whowechina/voltex_pico/doc/m2_8mm.jpg

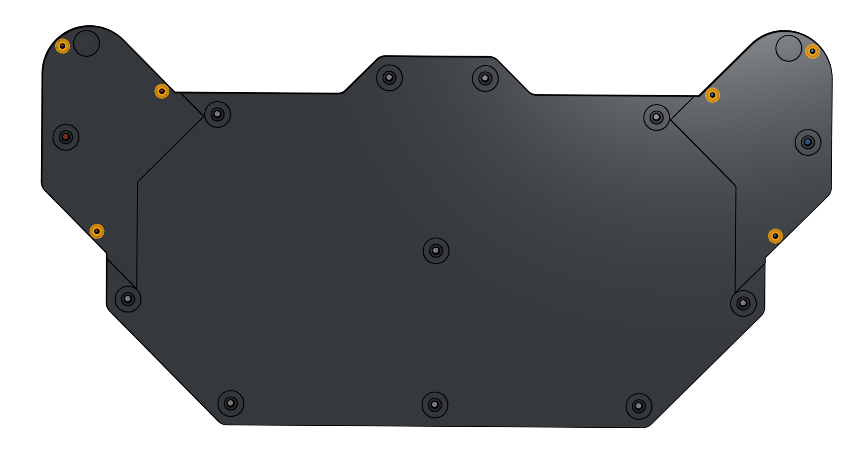
doc/m2_8mm.jpg
