whowechina/voltex_pico/PCB/jumbo/3dmodels/Raspberry Pi Pico-R3.step

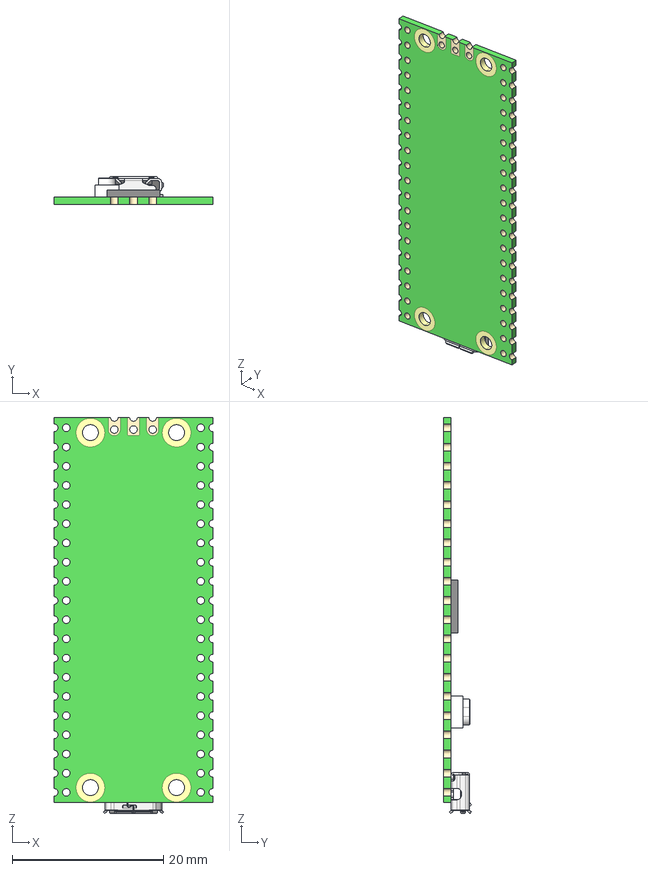
[picture p35: CAD file, 2026-08-16]
PCB/jumbo/3dmodels/Raspberry Pi Pico-R3.step
21.0 x 3.69 x 52.4 mm
PCB, Raspberry Pi Pico-R3
MicroUSB Port, Raspberry Pi Pico-R3
MicroUSB Port, Raspberry Pi Pico-R004
RP2040 Microcontroller, Raspberry Pi Pico-R3
SW1, Tact Switch, Raspberry Pi Pico-R3
