whowechina/voltex_pico/Production/3DPrint/Voltex Pico - Magnet Seat.stl

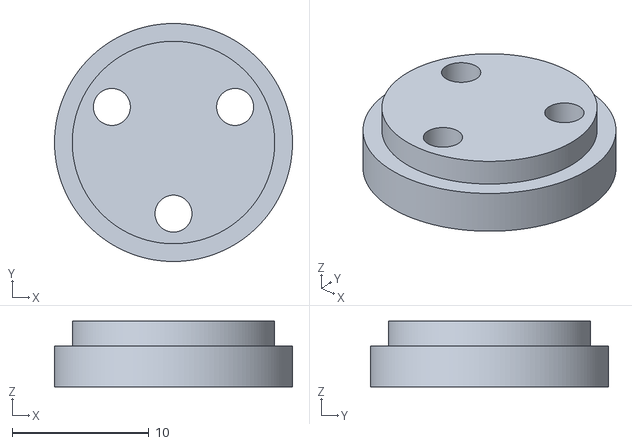
[picture p36: CAD file, 2025-12-08]
Production/3DPrint/Voltex Pico - Magnet Seat.stl
17.4 x 17.4 x 4.80
