whowechina/voltex_pico/PCB/jumbo/3dmodels/FPC6P_1.0mm_Bottom_Contact_Flip.stp

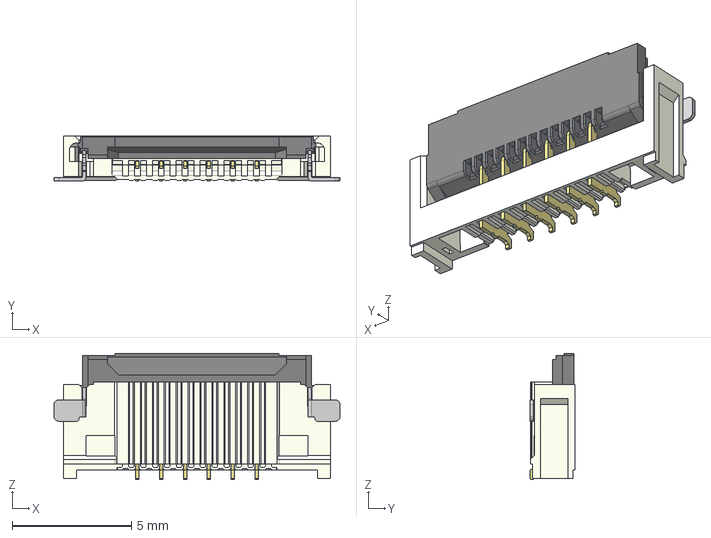
[picture p37: CAD file, 2026-03-18]
PCB/jumbo/3dmodels/FPC6P_1.0mm_Bottom_Contact_Flip.stp
12.0 x 1.90 x 5.30 mm
