whowechina/voltex_pico/Production/3DPrint/Voltex Pico - Left Wing Cover_Insert.stl

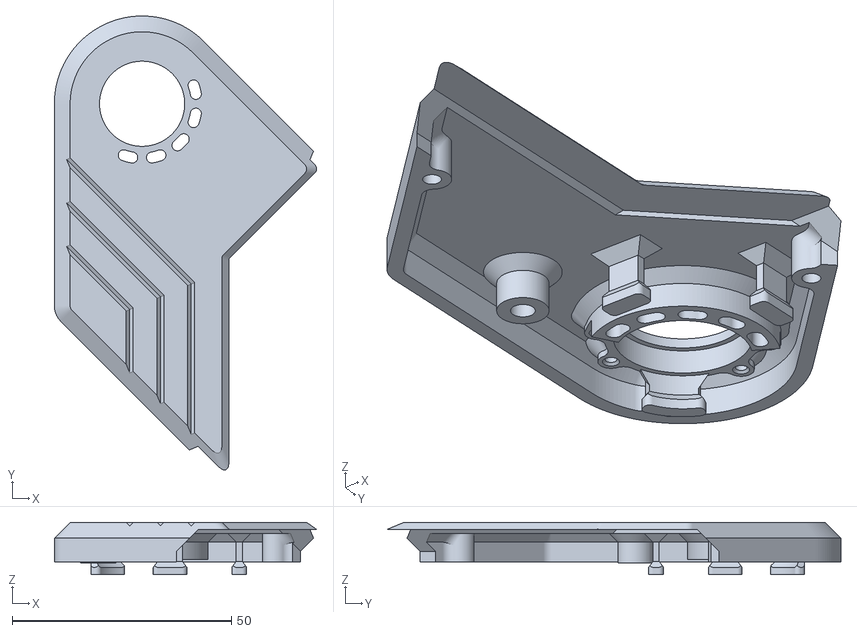
[picture p38: CAD file, 2025-12-07]
Production/3DPrint/Voltex Pico - Left Wing Cover_Insert.stl
59.8 x 103.4 x 11.9
