whowechina/voltex_pico/PCB/jumbo/3dmodels/skhhbva010.stp

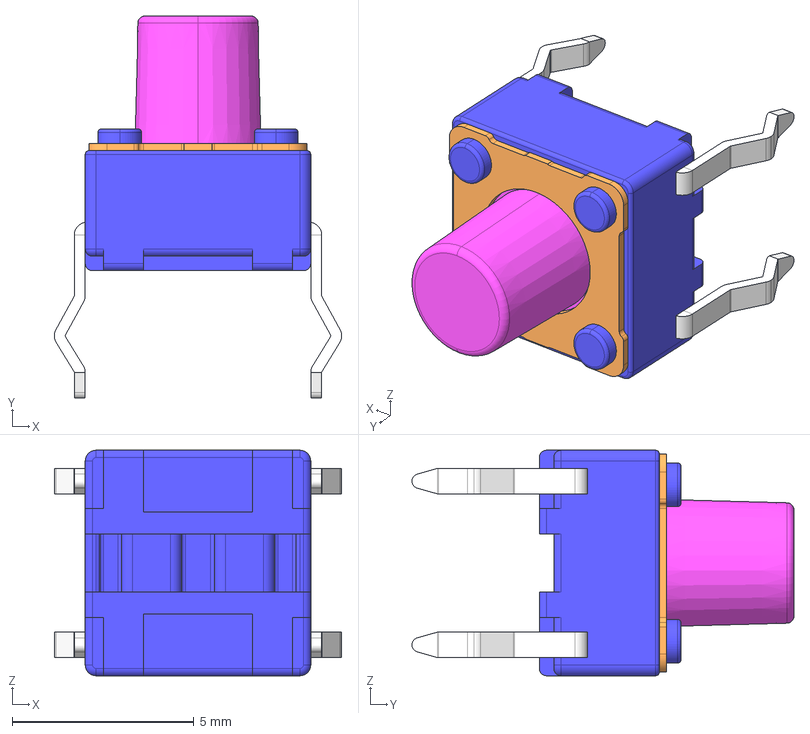
[picture p39: CAD file, 2025-06-14]
PCB/jumbo/3dmodels/skhhbva010.stp
7.90 x 10.5 x 6.20 mm
