whowechina/voltex_pico/Production/3DPrint/Voltex Pico - BT Choc V2_TallFix.stl

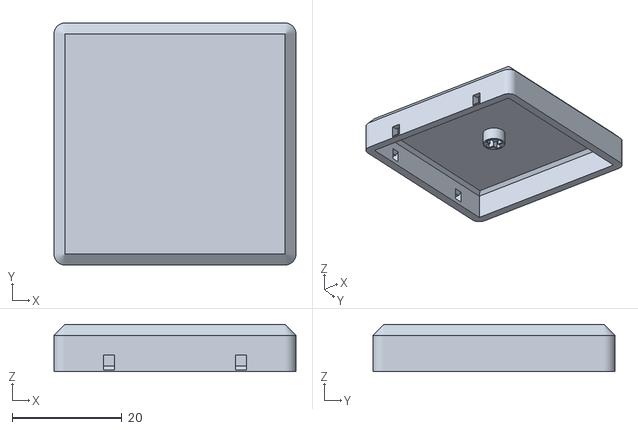
[picture p40: CAD file, 2025-12-07]
Production/3DPrint/Voltex Pico - BT Choc V2_TallFix.stl
44.0 x 44.0 x 8.60
