whowechina/voltex_pico/PCB/jumbo/3dmodels/skhhana010.stp

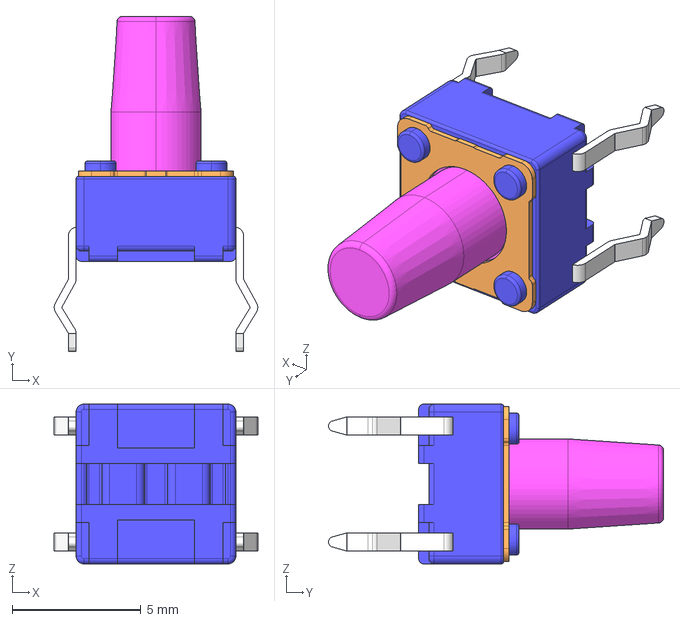
[picture p41: CAD file, 2025-06-14]
PCB/jumbo/3dmodels/skhhana010.stp
7.90 x 13.0 x 6.20 mm
