whowechina/voltex_pico/Production/3DPrint/Voltex Pico - FX-L Choc V2_TallFix.stl

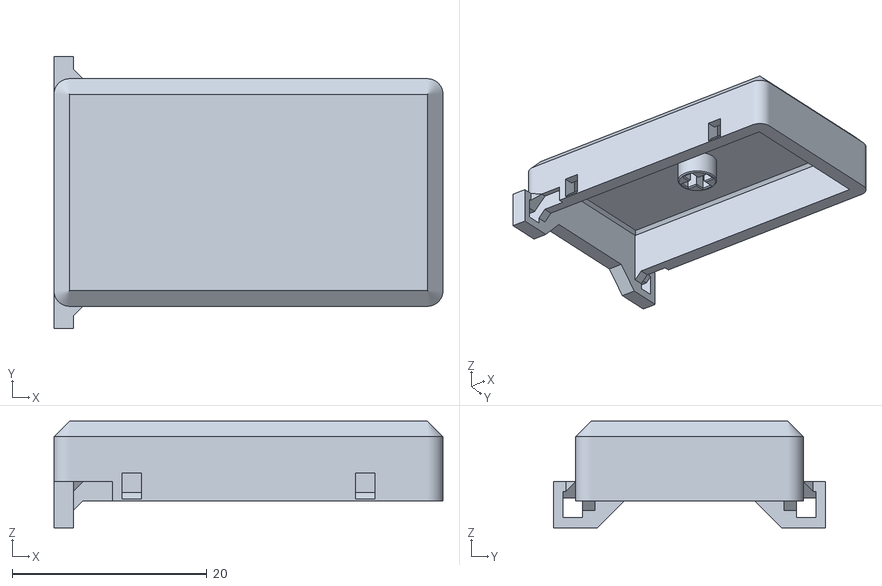
[picture p42: CAD file, 2025-12-07]
Production/3DPrint/Voltex Pico - FX-L Choc V2_TallFix.stl
40.0 x 28.0 x 11.0
