whowechina/voltex_pico/PCB/jumbo/3dmodels/SW_Hotswap_Kailh_MX.stp

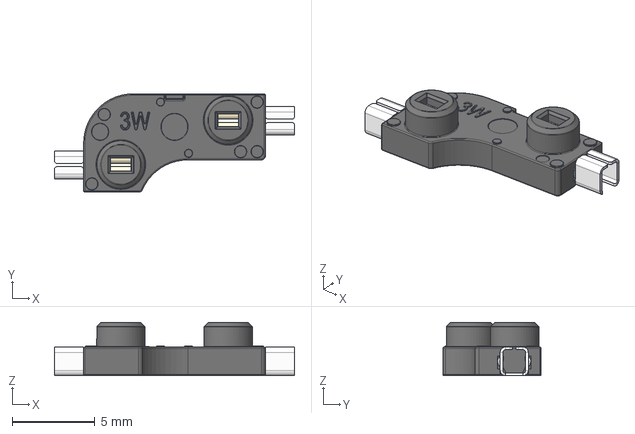
[picture p43: CAD file, 2025-05-26]
PCB/jumbo/3dmodels/SW_Hotswap_Kailh_MX.stp
14.5 x 5.95 x 3.22 mm
