whowechina/voltex_pico/PCB/jumbo/3dmodels/User Library-WS2812-4020.step

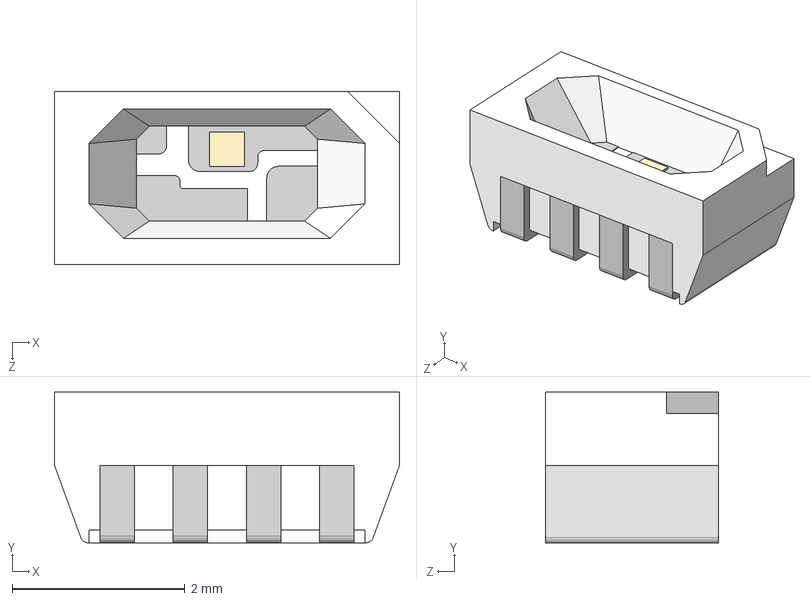
[picture p44: CAD file, 2025-05-26]
PCB/jumbo/3dmodels/User Library-WS2812-4020.step
4.00 x 1.75 x 2.00 mm
