whowechina/voltex_pico/PCB/jumbo/3dmodels/User Library-WS2812-2020.step

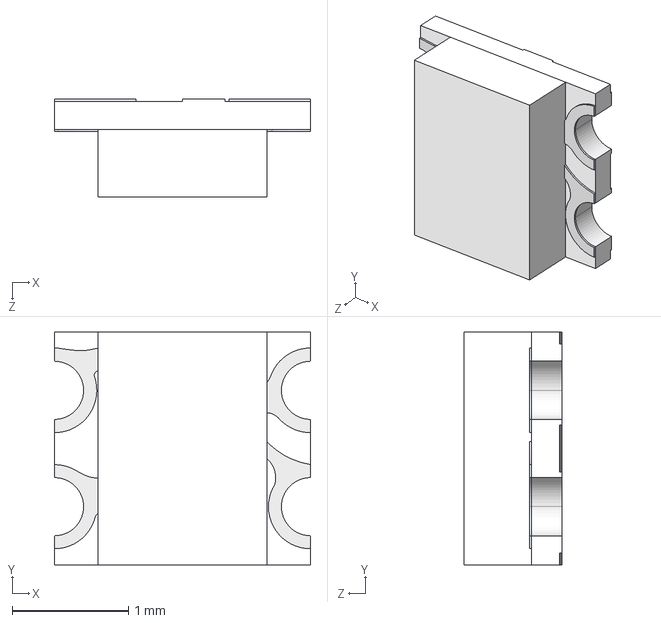
[picture p45: CAD file, 2025-05-26]
PCB/jumbo/3dmodels/User Library-WS2812-2020.step
2.20 x 2.00 x 0.84 mm
