whowechina/voltex_pico/PCB/jumbo/3dmodels/WS2812B.step

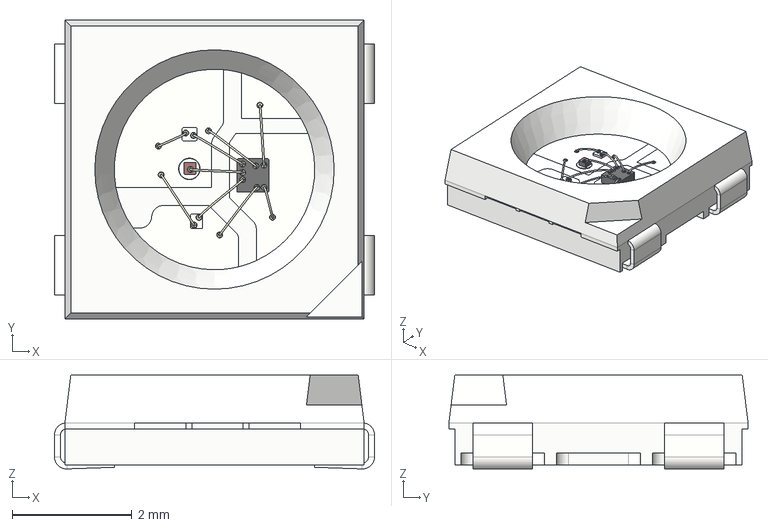
[picture p46: CAD file, 2025-05-26]
PCB/jumbo/3dmodels/WS2812B.step
5.35 x 5.00 x 1.57 mm
