whowechina/voltex_pico/PCB/jumbo/3dmodels/LED_WS2812_2020.step

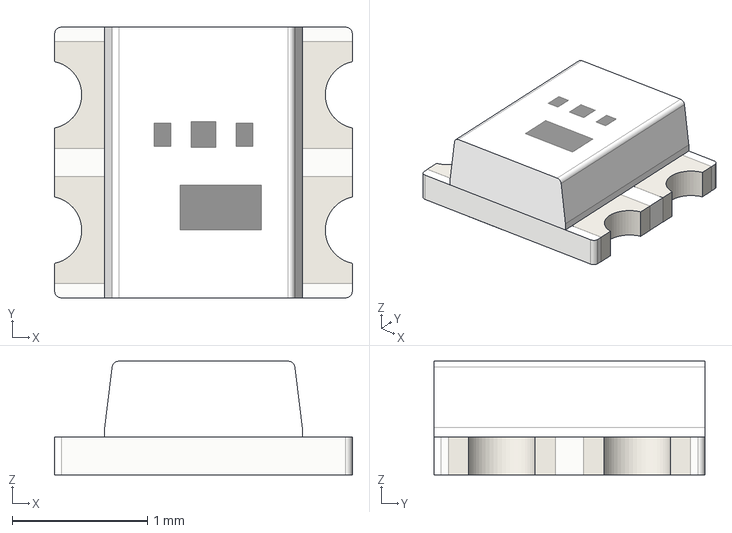
[picture p47: CAD file, 2025-05-26]
PCB/jumbo/3dmodels/LED_WS2812_2020.step
2.20 x 2.00 x 0.842 mm
