whowechina/voltex_pico/PCB/jumbo/3dmodels/WS2812-0807.STEP

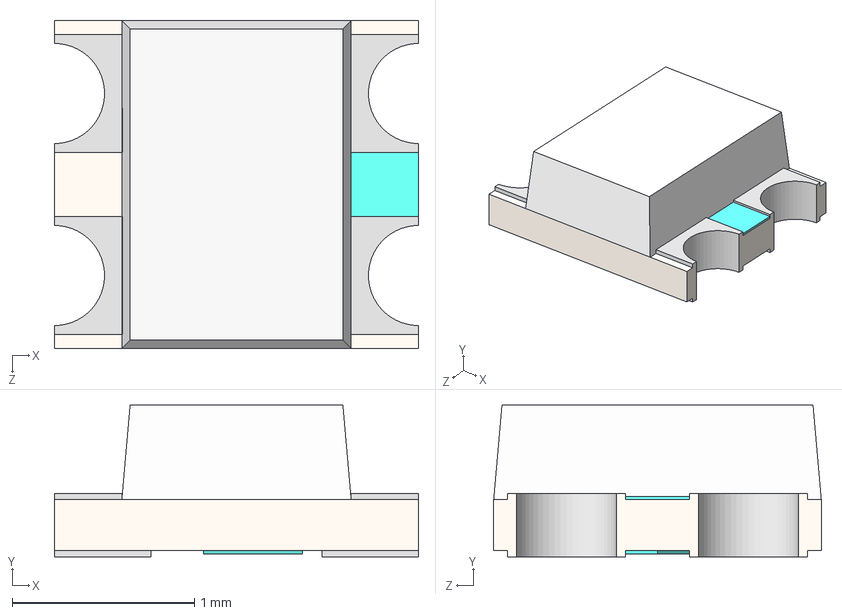
[picture p48: CAD file, 2025-05-26]
PCB/jumbo/3dmodels/WS2812-0807.STEP
2.00 x 0.835 x 1.80 mm
