whowechina/voltex_pico/Production/3DPrint/Voltex Pico - Support.stl

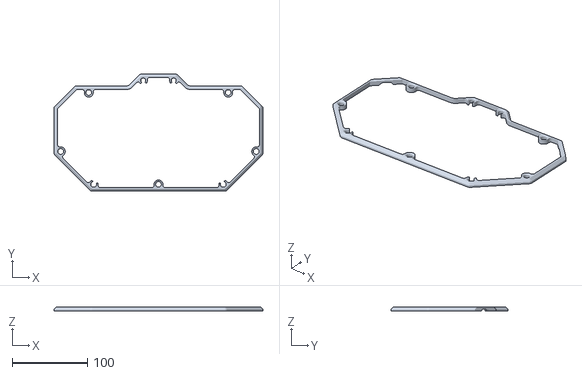
[picture p49: CAD file, 2025-06-24]
Production/3DPrint/Voltex Pico - Support.stl
278.2 x 156.2 x 5.40
