whowechina/voltex_pico/PCB/jumbo/3dmodels/WS2812-2020.STEP

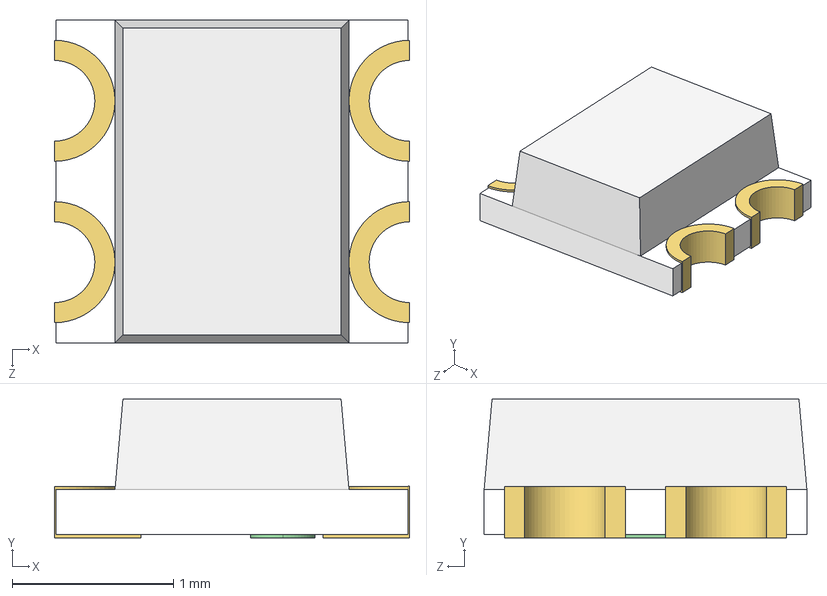
[picture p50: CAD file, 2025-05-26]
PCB/jumbo/3dmodels/WS2812-2020.STEP
2.20 x 0.86 x 2.00 mm
