whowechina/voltex_pico/Production/3DPrint/Voltex Pico - BT Choc V2.stl

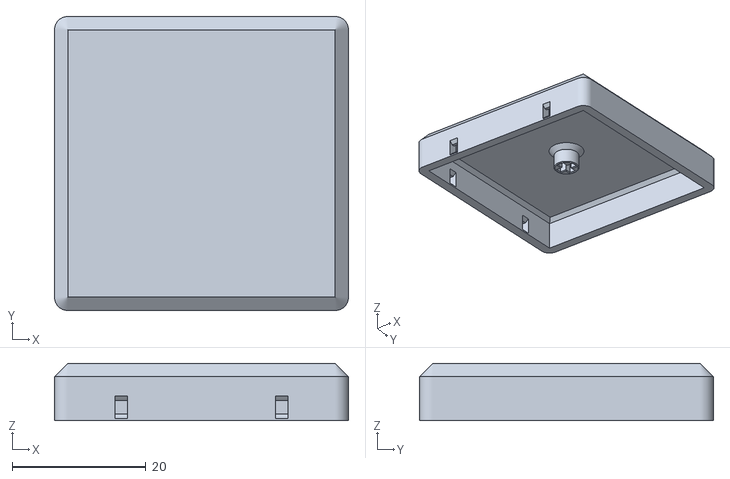
[picture p51: CAD file, 2025-06-24]
Production/3DPrint/Voltex Pico - BT Choc V2.stl
44.0 x 44.0 x 8.60
