whowechina/voltex_pico/PCB/jumbo/3dmodels/Kailh_PG1353.STEP

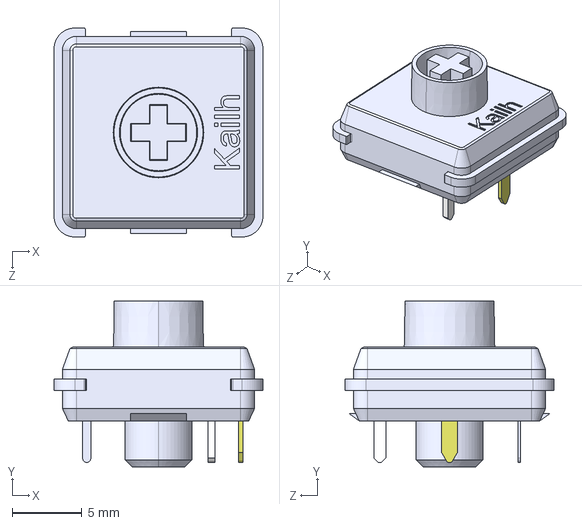
[picture p52: CAD file, 2025-05-26]
PCB/jumbo/3dmodels/Kailh_PG1353.STEP
15.0 x 11.9 x 15.0 mm
