whowechina/voltex_pico/PCB/jumbo/3dmodels/8002A.step

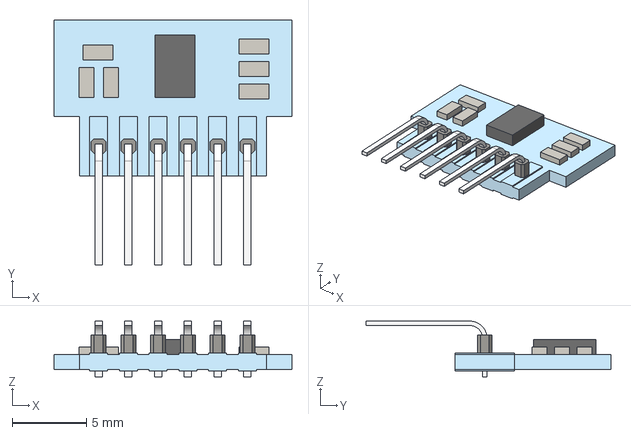
[picture p53: CAD file, 2025-05-26]
PCB/jumbo/3dmodels/8002A.step
16.0 x 16.5 x 3.75 mm
