whowechina/voltex_pico/PCB/jumbo/3dmodels/TRS Jack PJ-313.stp

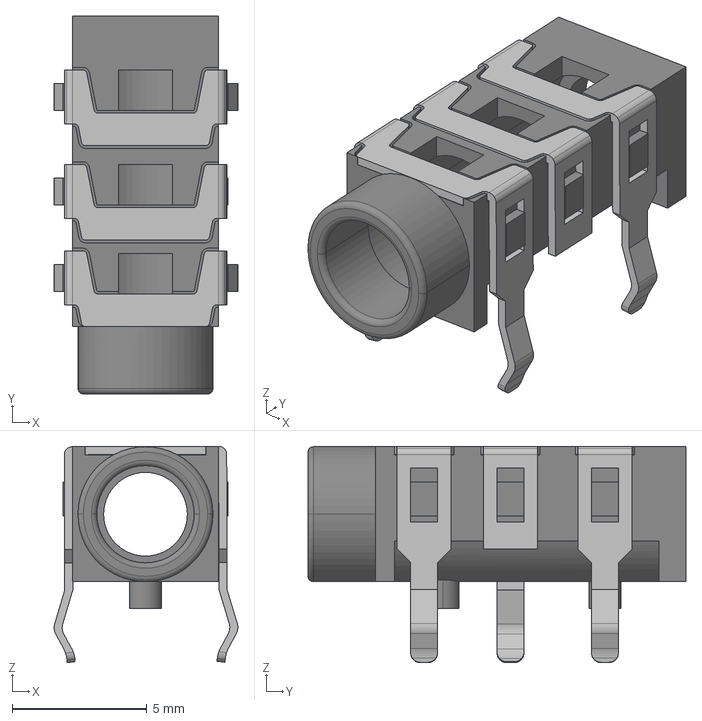
[picture p54: CAD file, 2025-05-26]
PCB/jumbo/3dmodels/TRS Jack PJ-313.stp
6.81 x 14.0 x 8.02 mm
