whowechina/voltex_pico/Production/3DPrint/Voltex Pico - Bearing Fixer.stl

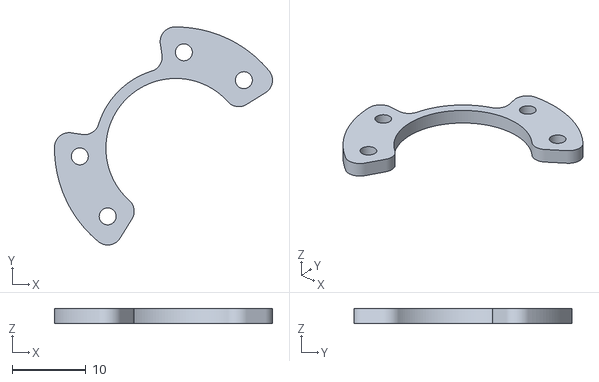
[picture p55: CAD file, 2025-06-24]
Production/3DPrint/Voltex Pico - Bearing Fixer.stl
29.7 x 29.7 x 2.00
