whowechina/voltex_pico/PCB/jumbo/3dmodels/SW_Hotswap_Kailh_Choc_V1.stp

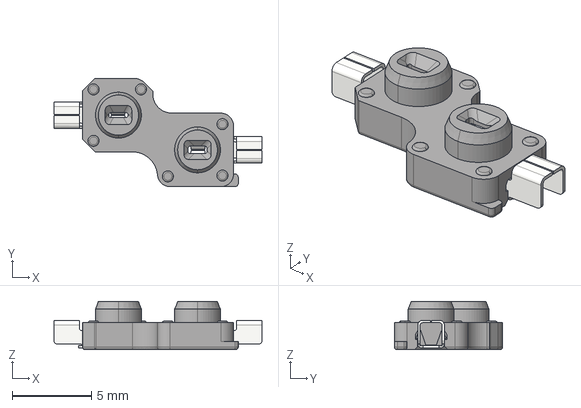
[picture p56: CAD file, 2025-05-26]
PCB/jumbo/3dmodels/SW_Hotswap_Kailh_Choc_V1.stp
13.2 x 6.85 x 3.05 mm
