whowechina/voltex_pico/PCB/jumbo/3dmodels/SM04B-SRSS-TB.STEP

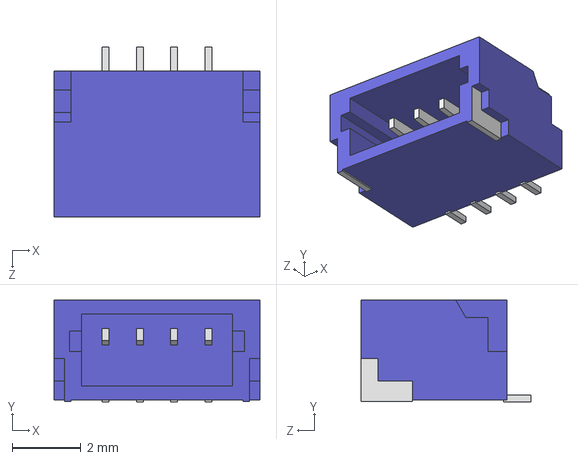
[picture p57: CAD file, 2025-05-26]
PCB/jumbo/3dmodels/SM04B-SRSS-TB.STEP
6.00 x 2.96 x 4.95 mm
