whowechina/voltex_pico/Production/3DPrint/Voltex Pico - Knob.stl

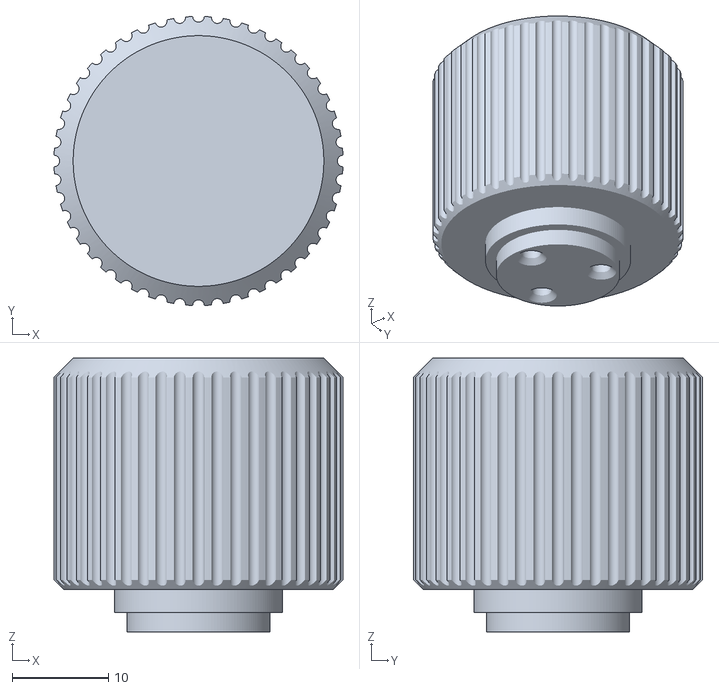
[picture p58: CAD file, 2025-06-24]
Production/3DPrint/Voltex Pico - Knob.stl
30.0 x 30.0 x 28.4
