whowechina/voltex_pico/PCB/jumbo/3dmodels/User Library-RGB1204.STEP

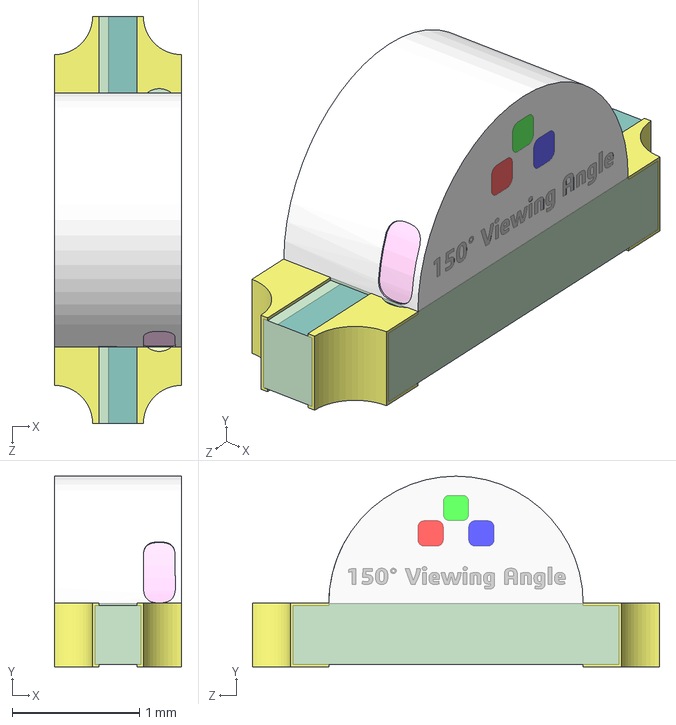
[picture p59: CAD file, 2025-05-26]
PCB/jumbo/3dmodels/User Library-RGB1204.STEP
1.00 x 1.50 x 3.20 mm
