whowechina/voltex_pico/PCB/jumbo/3dmodels/FPC0.5MM1.0H18P.step

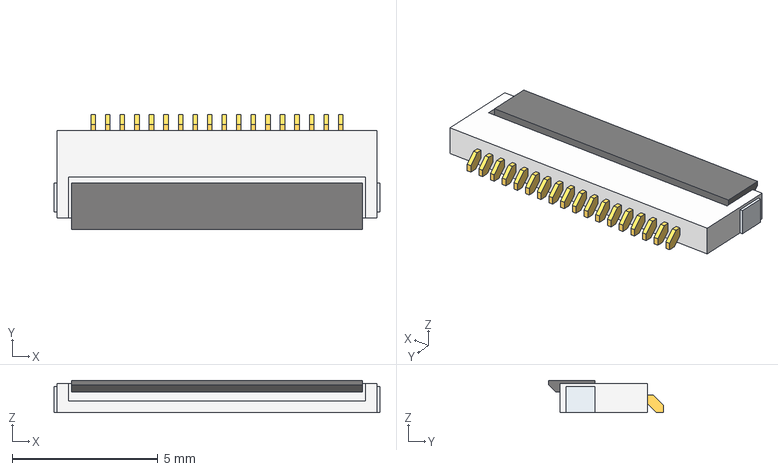
[picture p60: CAD file, 2025-05-26]
PCB/jumbo/3dmodels/FPC0.5MM1.0H18P.step
11.2 x 3.96 x 1.10 mm
