whowechina/voltex_pico/PCB/jumbo/3dmodels/EVQ-P1D05M.stp

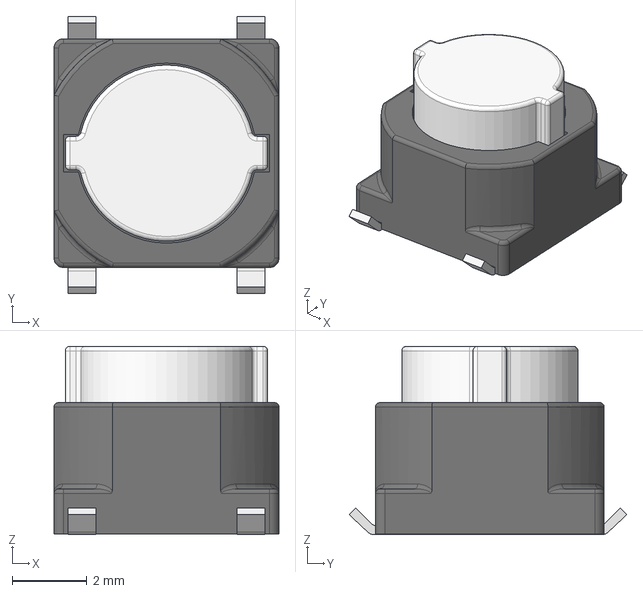
[picture p61: CAD file, 2025-05-26]
PCB/jumbo/3dmodels/EVQ-P1D05M.stp
6.00 x 7.40 x 5.03 mm
