whowechina/voltex_pico/PCB/jumbo/3dmodels/J 2835.step

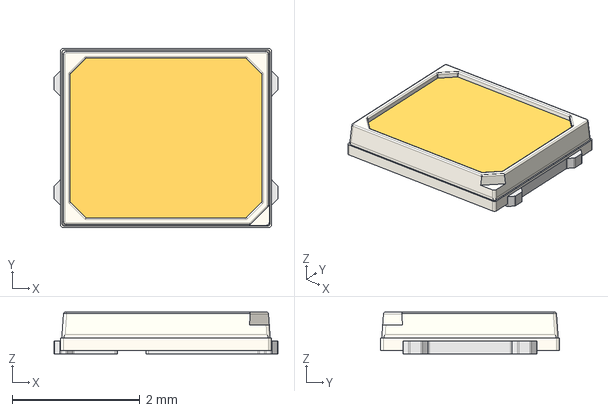
[picture p62: CAD file, 2025-05-26]
PCB/jumbo/3dmodels/J 2835.step
3.50 x 2.80 x 0.65 mm
