whowechina/voltex_pico/PCB/jumbo/3dmodels/SKSTAAE010.stp

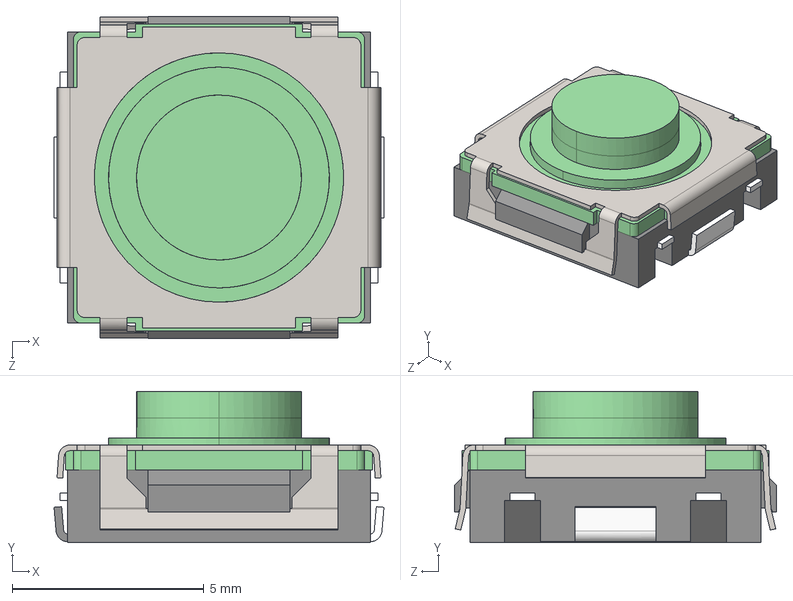
[picture p63: CAD file, 2025-05-26]
PCB/jumbo/3dmodels/SKSTAAE010.stp
8.61 x 3.95 x 8.40 mm
