whowechina/voltex_pico/PCB/jumbo/3dmodels/SS49E.step

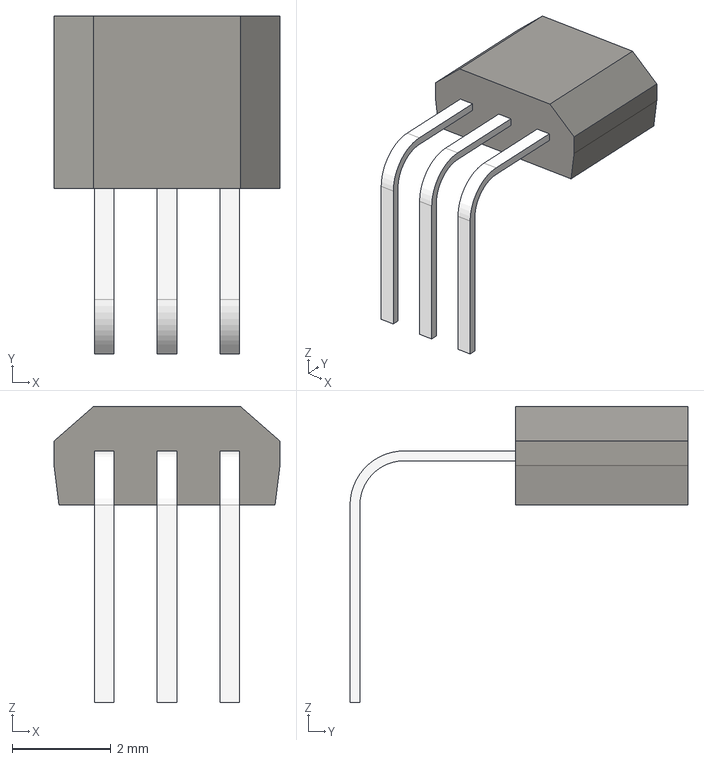
[picture p64: CAD file, 2025-05-26]
PCB/jumbo/3dmodels/SS49E.step
4.58 x 6.85 x 6.00 mm
