whowechina/voltex_pico/PCB/jumbo/3dmodels/dcdc_3to5.step

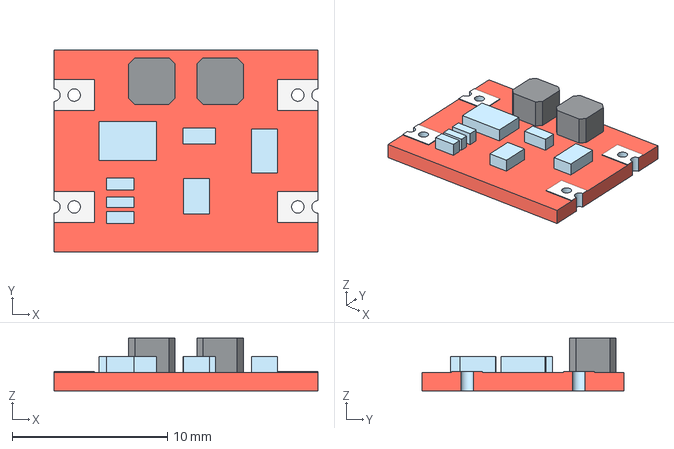
[picture p65: CAD file, 2025-05-26]
PCB/jumbo/3dmodels/dcdc_3to5.step
17.0 x 13.0 x 3.40 mm
