whowechina/voltex_pico/PCB/jumbo/3dmodels/Tact Switch 4.5mm SMT.step

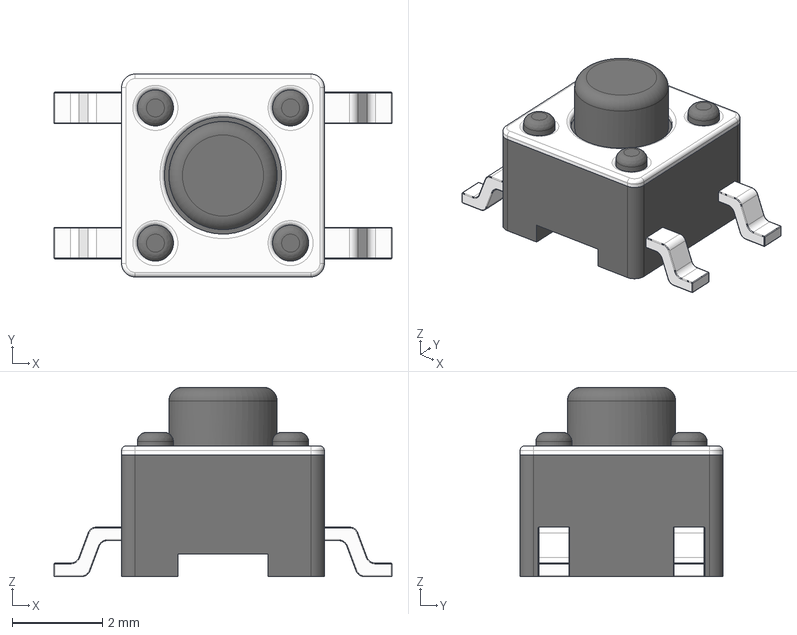
[picture p66: CAD file, 2025-05-26]
PCB/jumbo/3dmodels/Tact Switch 4.5mm SMT.step
7.50 x 4.50 x 4.20 mm
