whowechina/voltex_pico/PCB/jumbo/3dmodels/Button Cap.step

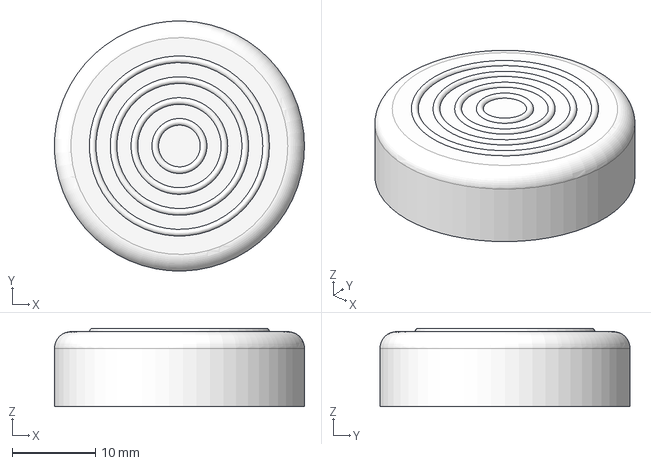
[picture p67: CAD file, 2025-05-26]
PCB/jumbo/3dmodels/Button Cap.step
30.0 x 30.0 x 9.40 mm
