whowechina/voltex_pico/PCB/jumbo/3dmodels/SMD WS2812B-3535.step

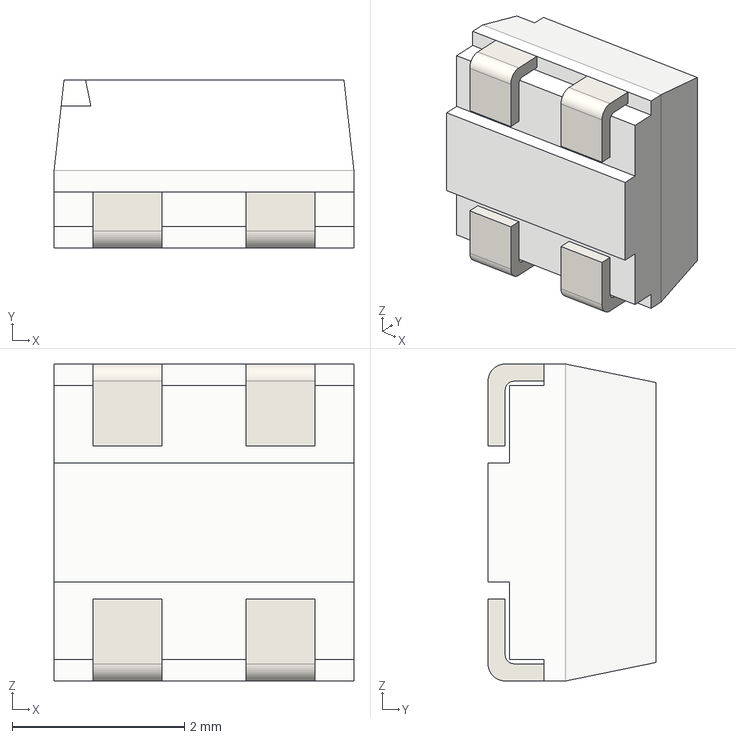
[picture p68: CAD file, 2025-05-26]
PCB/jumbo/3dmodels/SMD WS2812B-3535.step
3.48 x 1.95 x 3.68 mm
