whowechina/voltex_pico/PCB/jumbo/3dmodels/Kailh LP Choc PC Keycap.step

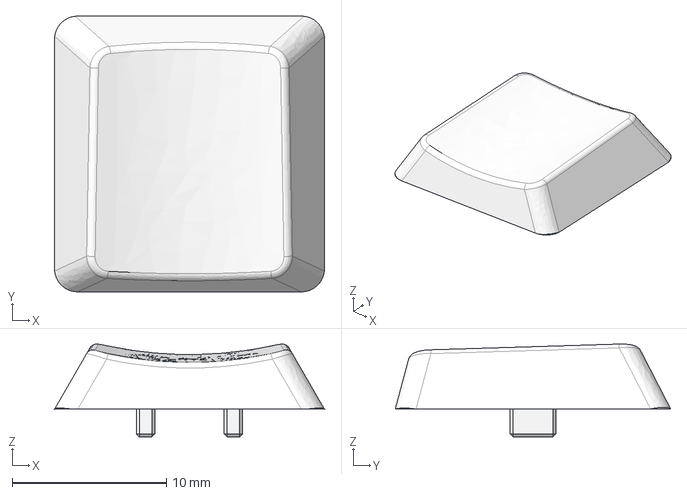
[picture p69: CAD file, 2025-05-26]
PCB/jumbo/3dmodels/Kailh LP Choc PC Keycap.step
17.5 x 17.9 x 6.03 mm
