whowechina/voltex_pico/PCB/jumbo/3dmodels/keypad_lgp.3mf

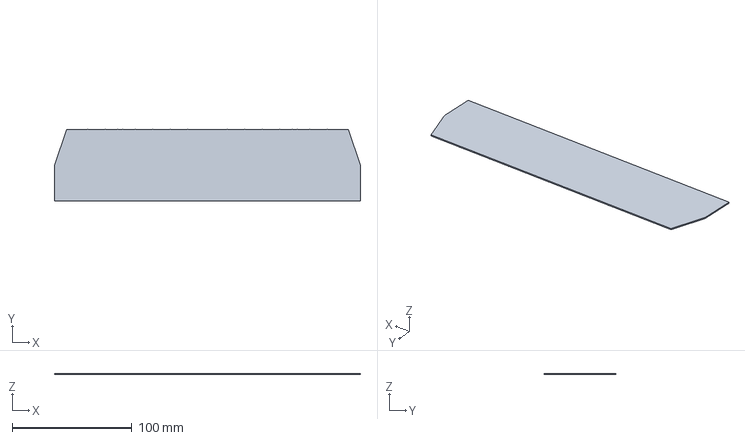
[picture p71: CAD file, 2025-05-26]
PCB/jumbo/3dmodels/keypad_lgp.3mf
256.0 x 60.0 x 1.00 mm
