whowechina/voltex_pico/PCB/jumbo/3dmodels/Slider.step

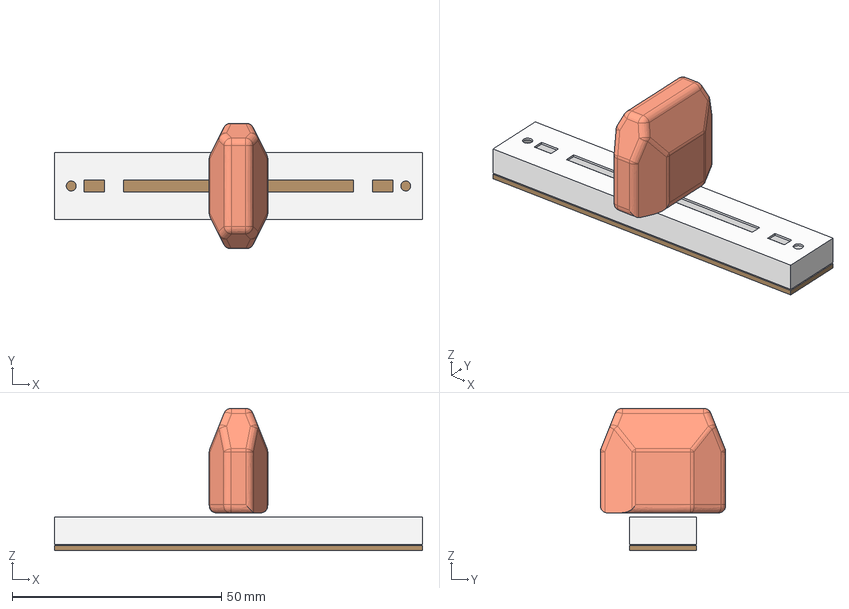
[picture p72: CAD file, 2025-05-26]
PCB/jumbo/3dmodels/Slider.step
88.0 x 30.0 x 34.0 mm
