whowechina/voltex_pico/PCB/jumbo/3dmodels/SW_Kailh_Choc_V1.stp

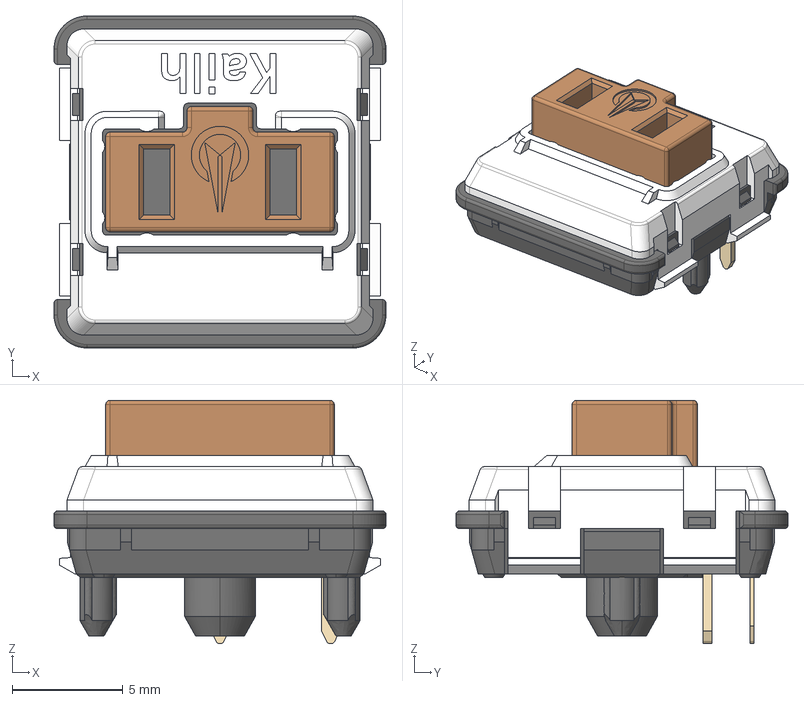
[picture p73: CAD file, 2025-05-26]
PCB/jumbo/3dmodels/SW_Kailh_Choc_V1.stp
15.0 x 15.0 x 11.0 mm
