whowechina/voltex_pico/PCB/jumbo/3dmodels/chu_keypad_lgp.step

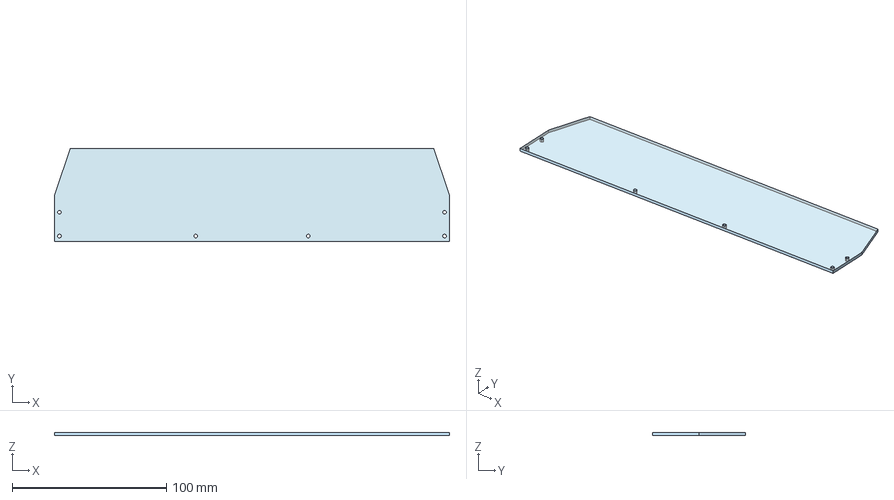
[picture p74: CAD file, 2025-05-26]
PCB/jumbo/3dmodels/chu_keypad_lgp.step
256.0 x 60.0 x 2.00 mm
