whowechina/voltex_pico/PCB/jumbo/3dmodels/Geki_Slider.step

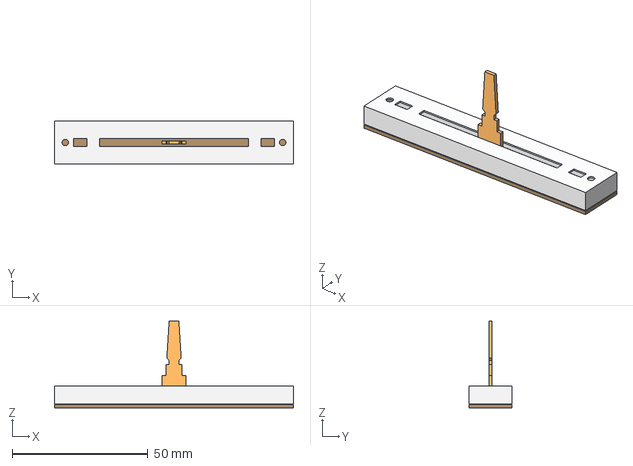
[picture p75: CAD file, 2025-05-26]
PCB/jumbo/3dmodels/Geki_Slider.step
88.0 x 16.0 x 32.0 mm
