whowechina/voltex_pico/PCB/jumbo/3dmodels/pn5180.step

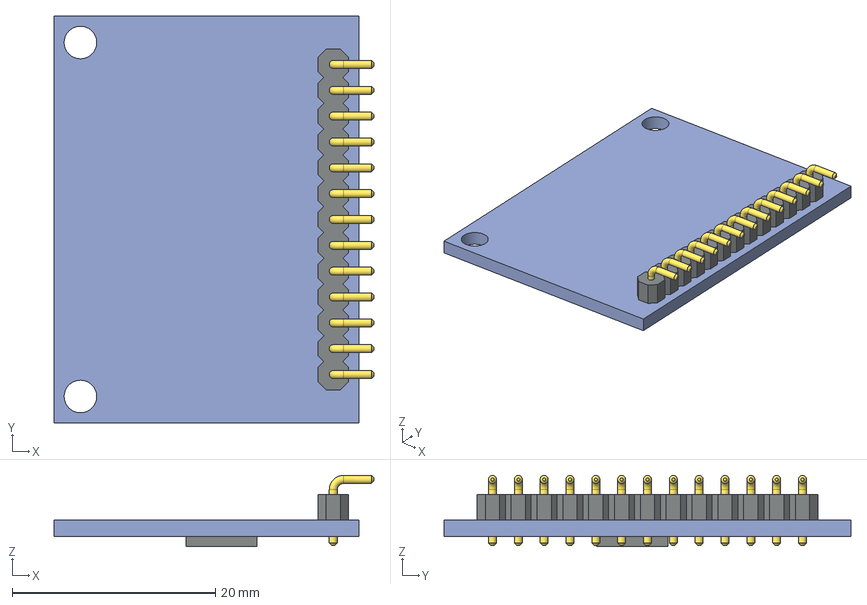
[picture p76: CAD file, 2025-05-26]
PCB/jumbo/3dmodels/pn5180.step
31.5 x 40.0 x 7.00 mm
