whowechina/voltex_pico/PCB/jumbo/3dmodels/SKPMAM.STEP

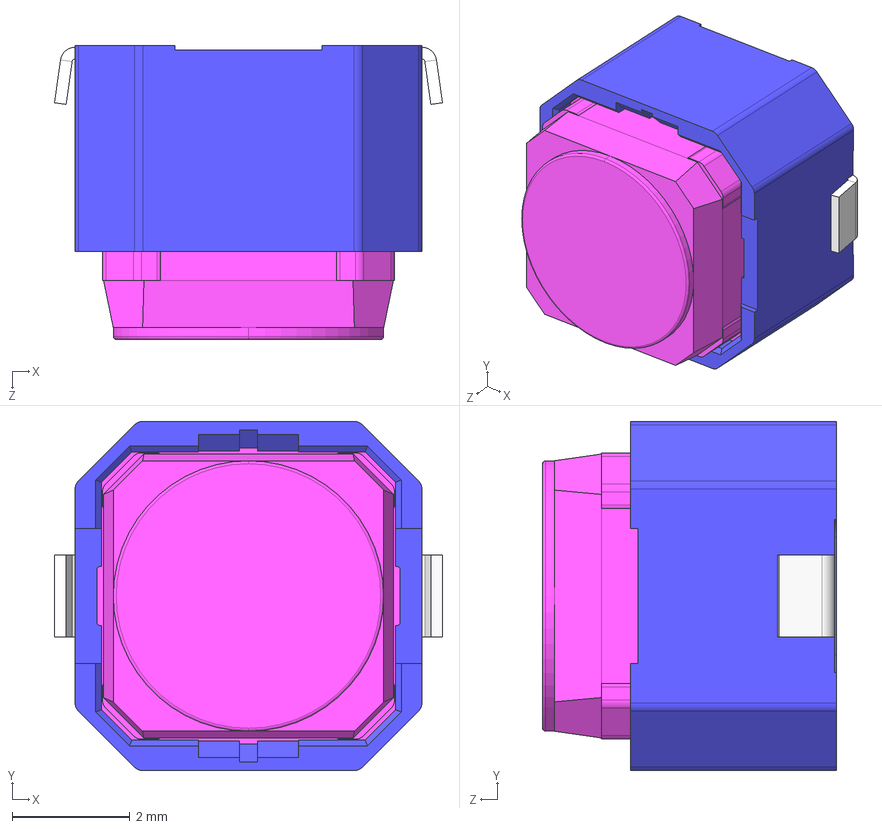
[picture p77: CAD file, 2025-05-26]
PCB/jumbo/3dmodels/SKPMAM.STEP
6.60 x 5.94 x 5.00 mm
