whowechina/voltex_pico/PCB/jumbo/3dmodels/User Library-PTS645SL95SMTR92-LFS.STEP

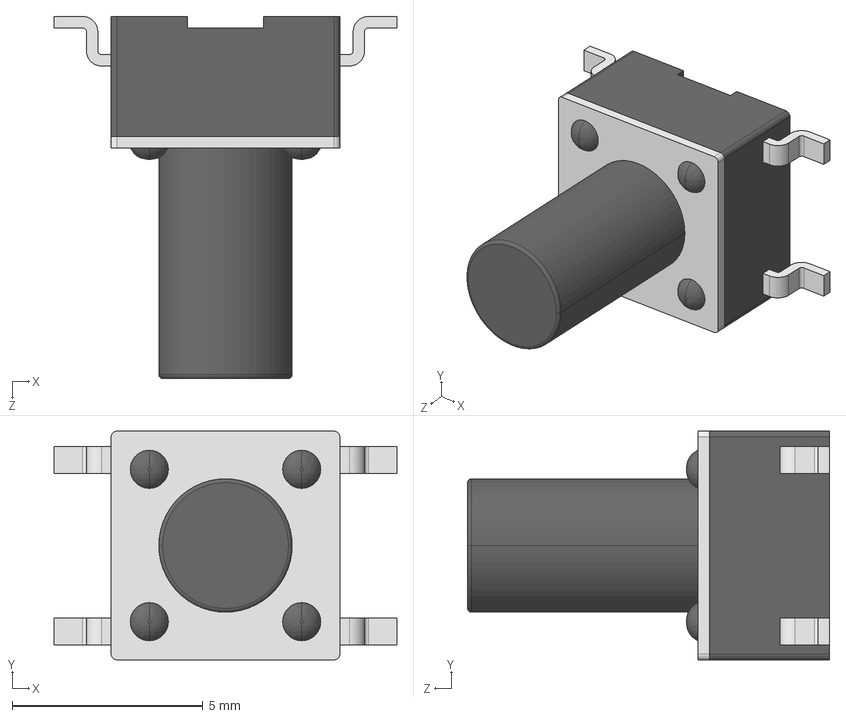
[picture p78: CAD file, 2025-05-26]
PCB/jumbo/3dmodels/User Library-PTS645SL95SMTR92-LFS.STEP
9.00 x 6.00 x 9.50 mm
