whowechina/voltex_pico/PCB/jumbo/3dmodels/SKRRABE010.stp

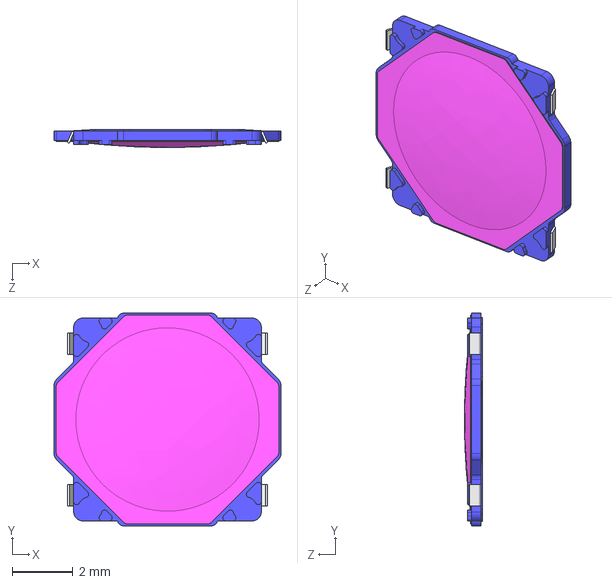
[picture p79: CAD file, 2025-05-26]
PCB/jumbo/3dmodels/SKRRABE010.stp
7.50 x 7.03 x 0.6 mm
