whowechina/voltex_pico/PCB/jumbo/3dmodels/SPEAKER_SMD_1340.STEP

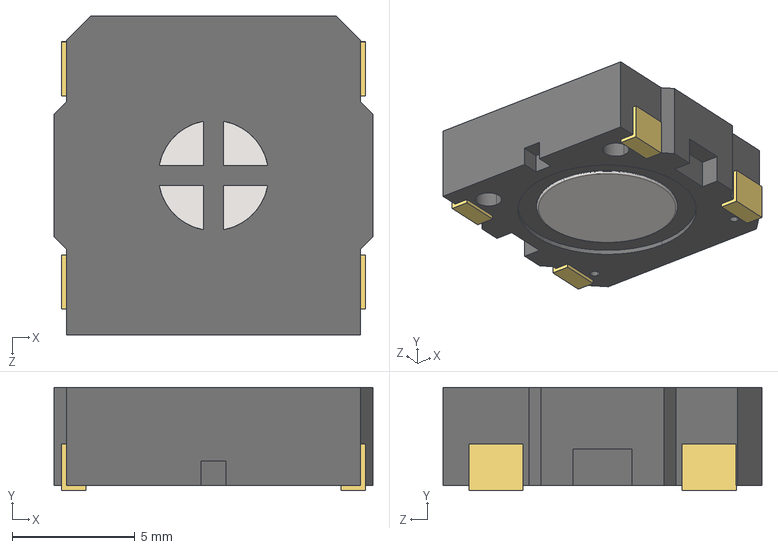
[picture p80: CAD file, 2025-05-26]
PCB/jumbo/3dmodels/SPEAKER_SMD_1340.STEP
13.0 x 4.20 x 13.0 mm
