whowechina/voltex_pico/PCB/jumbo/3dmodels/gp2y0e03.3mf

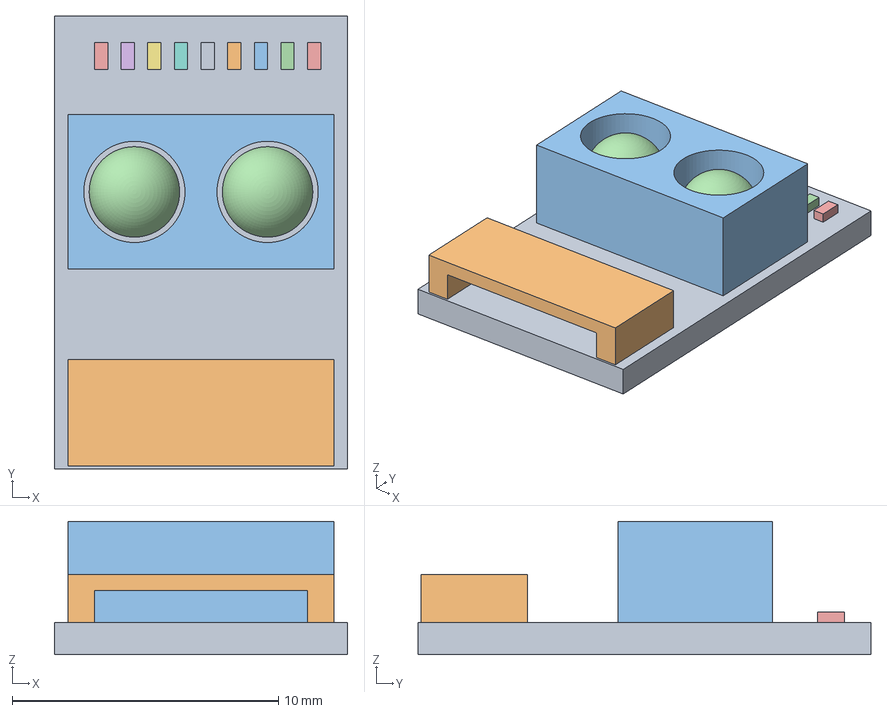
[picture p81: CAD file, 2025-05-26]
PCB/jumbo/3dmodels/gp2y0e03.3mf
11.0 x 17.0 x 5.00 mm
