whowechina/voltex_pico/PCB/jumbo/3dmodels/geki_button.step

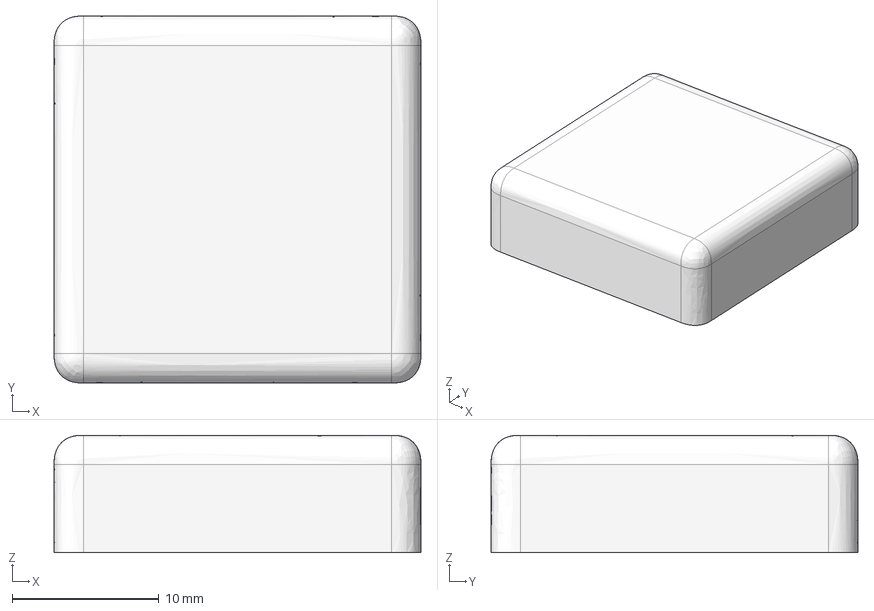
[picture p82: CAD file, 2025-05-26]
PCB/jumbo/3dmodels/geki_button.step
25.0 x 25.0 x 8.00 mm
