whowechina/voltex_pico/PCB/jumbo/3dmodels/mpr121_breakout_v13.stl

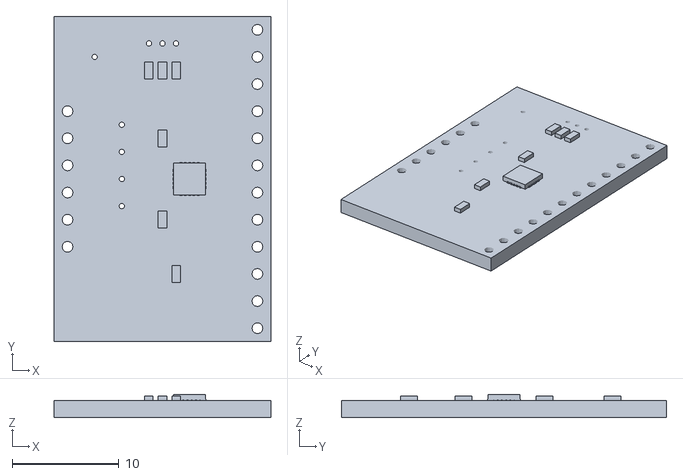
[picture p83: CAD file, 2025-05-26]
PCB/jumbo/3dmodels/mpr121_breakout_v13.stl
20.3 x 30.5 x 2.20
