whowechina/voltex_pico/firmware/src/config.c

/*
 * Controller Config and Runtime Data
 * WHowe <github.com/whowechina>
 * 
 * Config is a global data structure that stores all the configuration
 * Runtime is something to share between files.
 */

#include "config.h"
#include "save.h"

voltex_cfg_t *voltex_cfg;

static voltex_cfg_t default_cfg = {
    .calibrated = {
        .up = {3600, 3600, 3600, 3600, 3600, 3600},
        .down = {2400, 2400, 2400, 2400, 2400, 2400},
    },
    .knob = {
        .units_per_turn = 144,
    },
    .light = {
        .level = 128,
    },
    .trigger = {
        .on = {12, 12, 12, 12, 12, 12},
        .off = {20, 20, 20, 20, 20, 20},
    },
};

voltex_runtime_t voltex_runtime;

static void config_loaded()
{
    for (int i = 0; i < 6; i++) {
        if (voltex_cfg->trigger.on[i] > 35) {
            voltex_cfg->trigger.on[i] = 35;
        }
        if (voltex_cfg->trigger.off[i] > 35) {
            voltex_cfg->trigger.off[i] = 35;
        }
    }

    if (voltex_cfg->knob.units_per_turn == 0) {
        voltex_cfg->knob.units_per_turn = 80;
    }

    config_changed();
}

void config_changed()
{
    save_request(false);
}

void config_factory_reset()
{
    *voltex_cfg = default_cfg;
    save_request(true);
}

void config_init()
{
    voltex_cfg = (voltex_cfg_t *)save_alloc(sizeof(*voltex_cfg), &default_cfg, config_loaded);
}
